h4ctar/retro-gauge/images/indicators/neutral.png

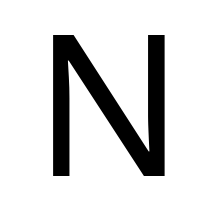
images/indicators/neutral.png
