h4ctar/retro-gauge/firmware/include/timer.h

#ifndef _TIMER_H
#define _TIMER_H

#include <stdint.h>

#define MILLISECONDS_PER_SECOND 1000.0
#define MICROSECONDS_PER_SECOND 1000000.0

void initTimer();
uint32_t millis();
uint32_t micros();

#endif
